JZRod/Project-NEO-Zia/Revisions/REV 4/Project NEO Zia REV 4.step

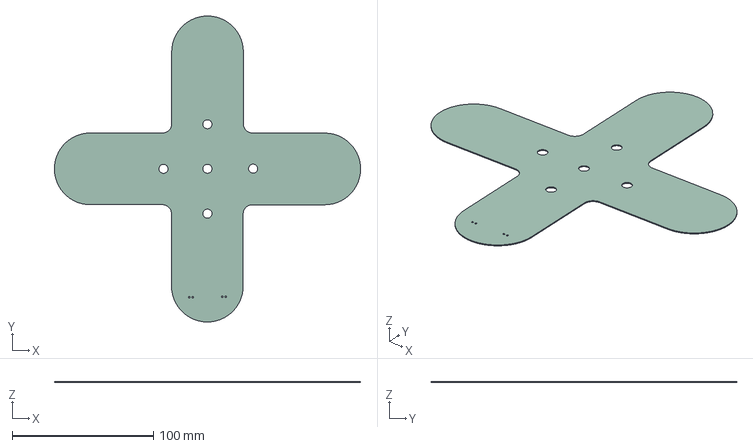
[picture p23: CAD file, 2025-10-10, an earlier design]
Revisions/REV 4/Project NEO Zia REV 4.step
216.9 x 216.8 x 0.61 mm
