JZRod/Project-NEO-Zia/assets/Wiring Diagrams/wiring diagram.kicad_sch

## KiCad design assets/Wiring Diagrams/wiring diagram.kicad_sch (2025-10-10)

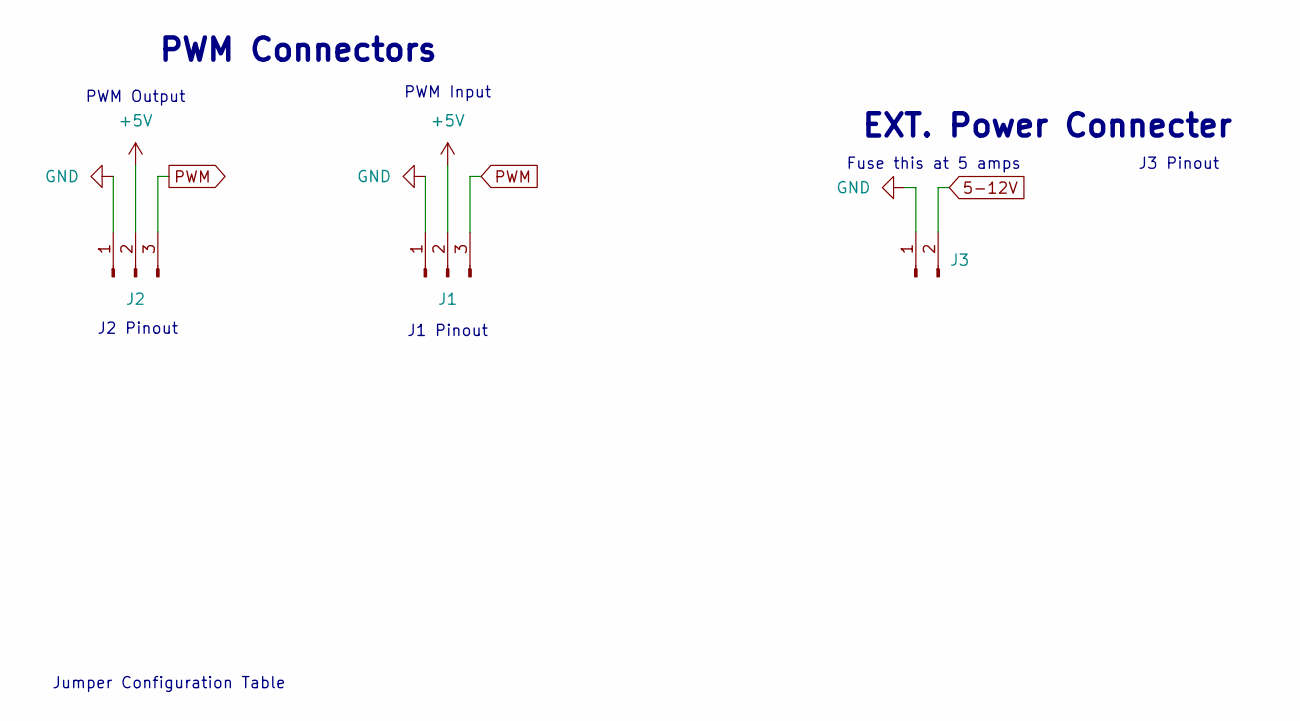
[picture p26: schematic wiring diagram.kicad_sch]

Parts:
J1, J2: Conn_01x03_Pin
J3: Conn_01x02_Pin

Connections:
5-12V: J3.2
+5V: J1.2, J2.2
GND: J1.1, J2.1, J3.1
PWM: J1.3, J2.3

Notes on the sheet:
J2 Pinout
PWM Output
PWM Input
J1 Pinout
Jumper Configuration Table
J3 Pinout
EXT. Power Connecter
Fuse this at 5 amps
PWM Connectors
